bessszilard/RTT_G/arduino_Eagle_PCB/123.png

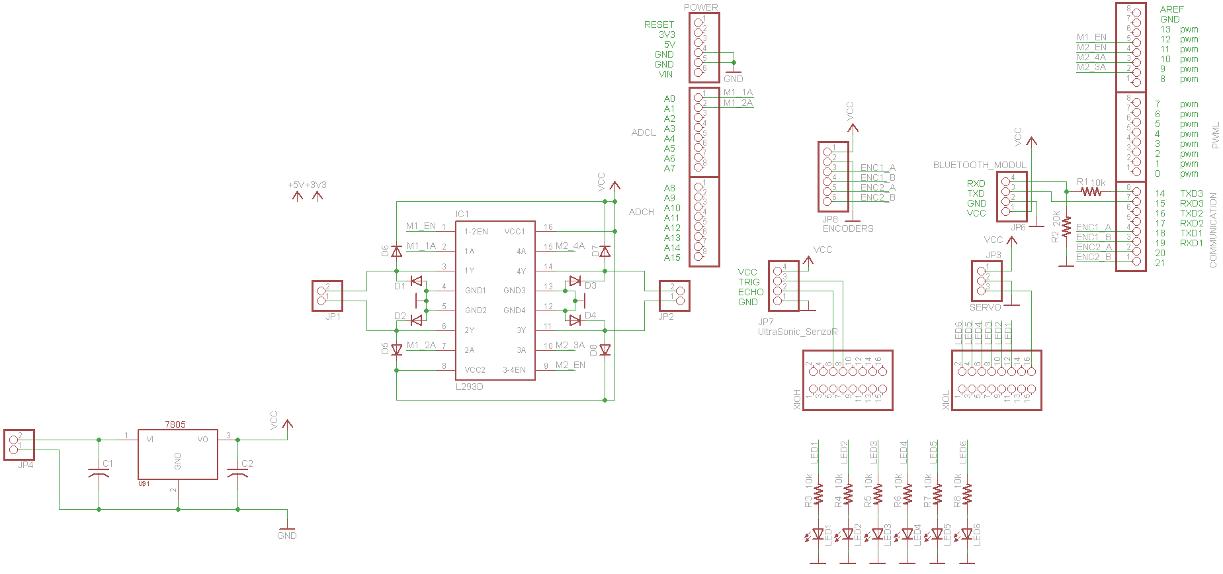
arduino_Eagle_PCB/123.png
